joelamichaelis/8x8x8_RGB_LED_CUBE/Documents/Steve Manley Resources/PCB Layouts/Base PCB All Layers with Copper Fill as Viewed from Underneith - Rev 1.1.pdf

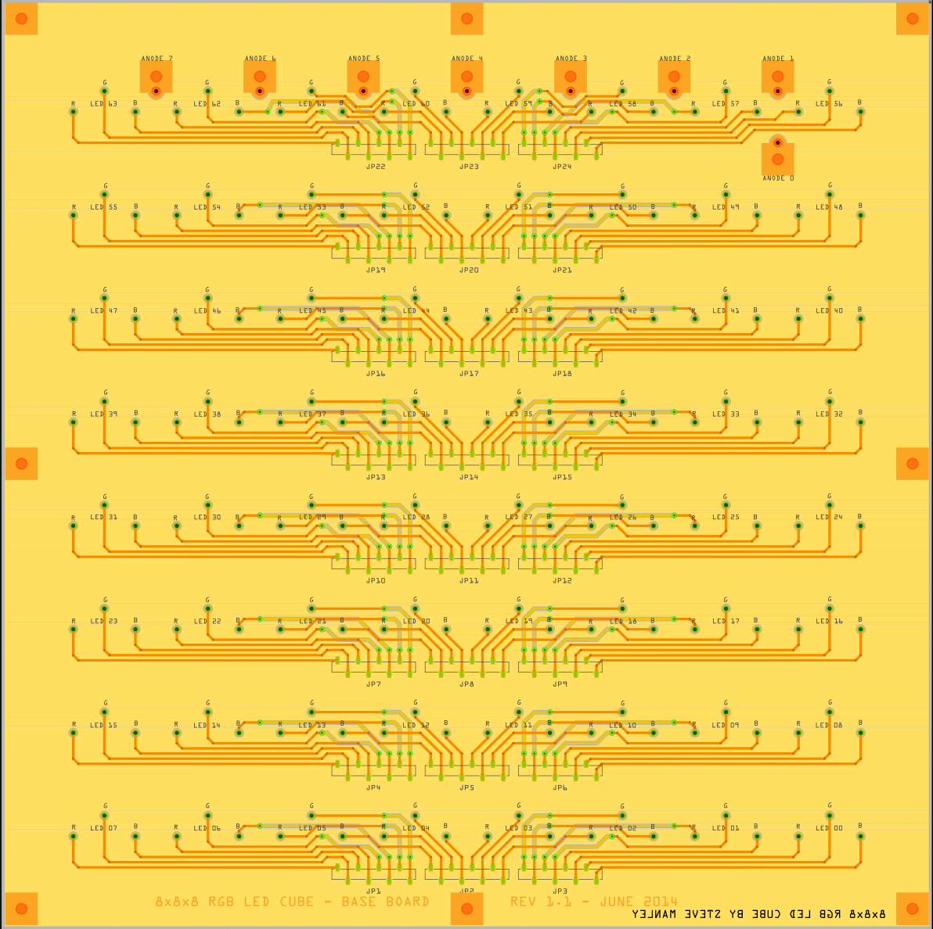
[picture p3: page 1]
