joelamichaelis/8x8x8_RGB_LED_CUBE/Documents/Steve Manley Resources/PCB Layouts/Base PCB Topside with Copper Fill as Viewed from Above - Rev 1.1.pdf

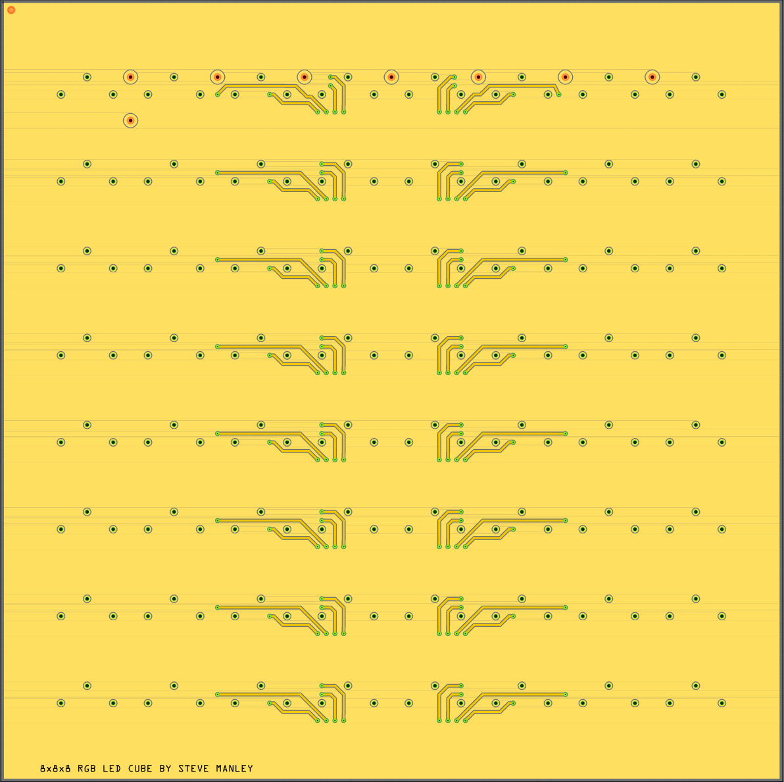
[picture p4: page 1]
