joelamichaelis/8x8x8_RGB_LED_CUBE/Documents/Steve Manley Resources/PCB Layouts/Base PCB Topside without Copper Fill as Viewed from Above - Rev 1.1.pdf

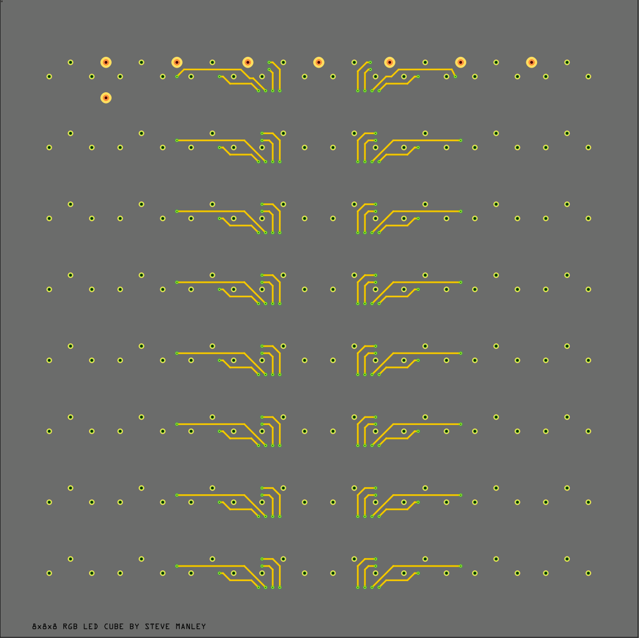
[picture p5: page 1]
