joelamichaelis/8x8x8_RGB_LED_CUBE/Documents/Steve Manley Resources/PCB Layouts/Base PCB Underside as Viewed from Underneith - Rev 1.1.pdf

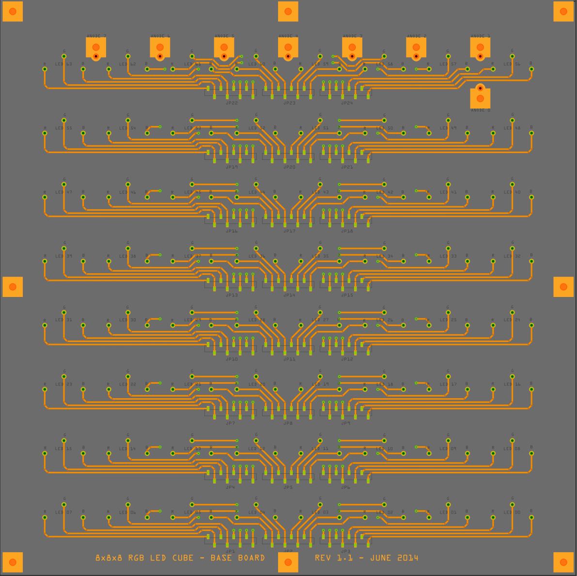
[picture p6: page 1]
