joelamichaelis/8x8x8_RGB_LED_CUBE/Datasheets/Microprocessor/STM32 vs ATmega328P.PNG

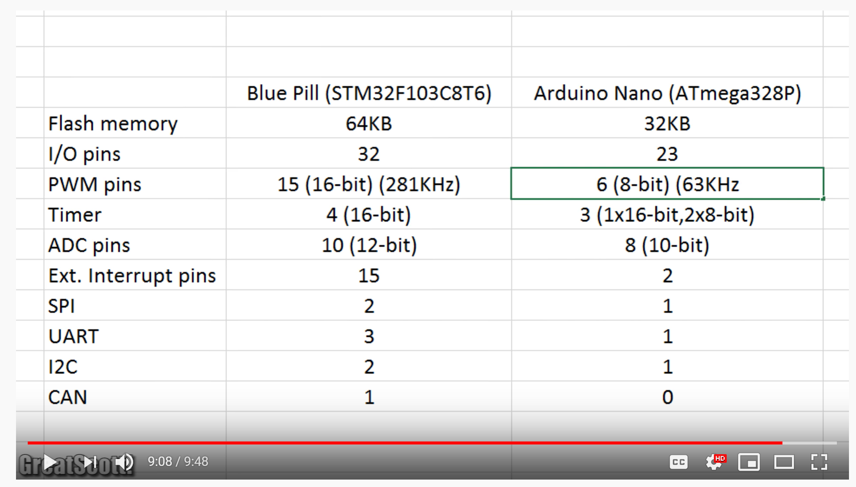
Datasheets/Microprocessor/STM32 vs ATmega328P.PNG
