joelamichaelis/8x8x8_RGB_LED_CUBE/Documents/Misc/firmware alphabet.jpg

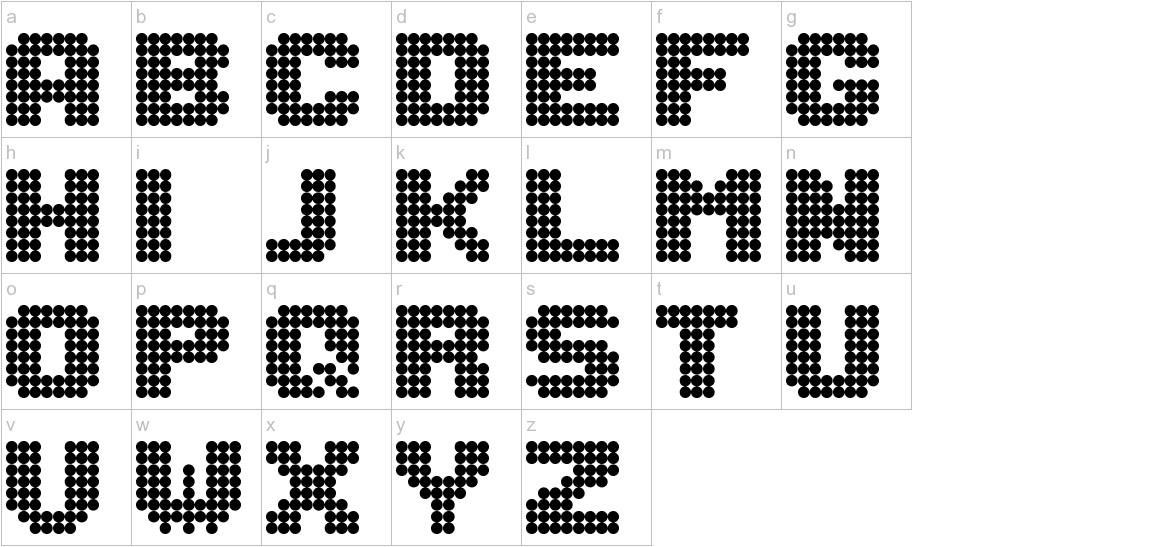
Documents/Misc/firmware alphabet.jpg
