joelamichaelis/8x8x8_RGB_LED_CUBE/Firmware/Misc/I2C_LCD_Development/lcd_addreses.jpg

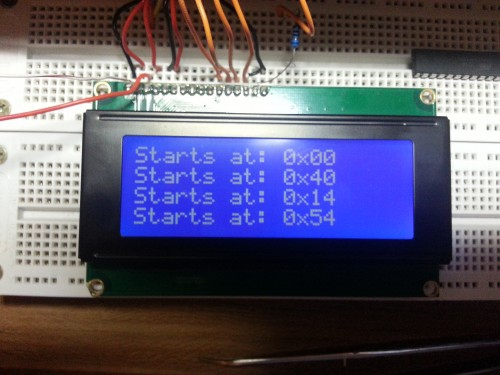
Firmware/Misc/I2C_LCD_Development/lcd_addreses.jpg
