joelamichaelis/8x8x8_RGB_LED_CUBE/Firmware/Misc/STM32 Personal Firmware/cube/USB_OTG_Clock.PNG

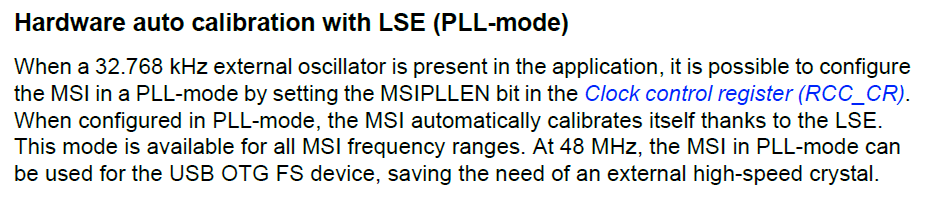
Firmware/Misc/STM32 Personal Firmware/cube/USB_OTG_Clock.PNG
