joelamichaelis/8x8x8_RGB_LED_CUBE/Project Photos/Phase 2 Photos/Mechanical Renders/2020-03-29 CubeBaseFull_FRONT.ipt.png

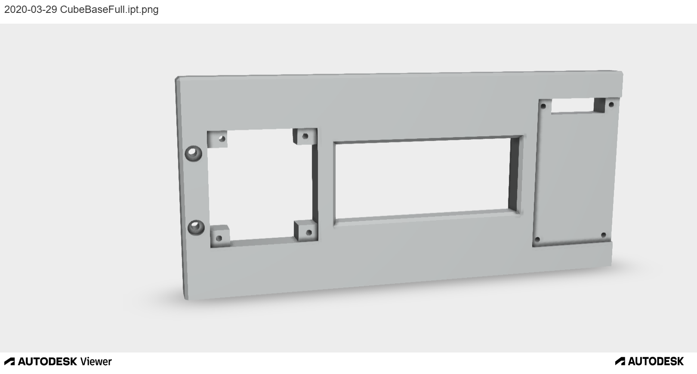
Project Photos/Phase 2 Photos/Mechanical Renders/2020-03-29 CubeBaseFull_FRONT.ipt.png
