joelamichaelis/8x8x8_RGB_LED_CUBE/Project Photos/Phase 2 Photos/Mechanical Renders/2020-04-11 CubeBaseSkeleton_FRONT.png

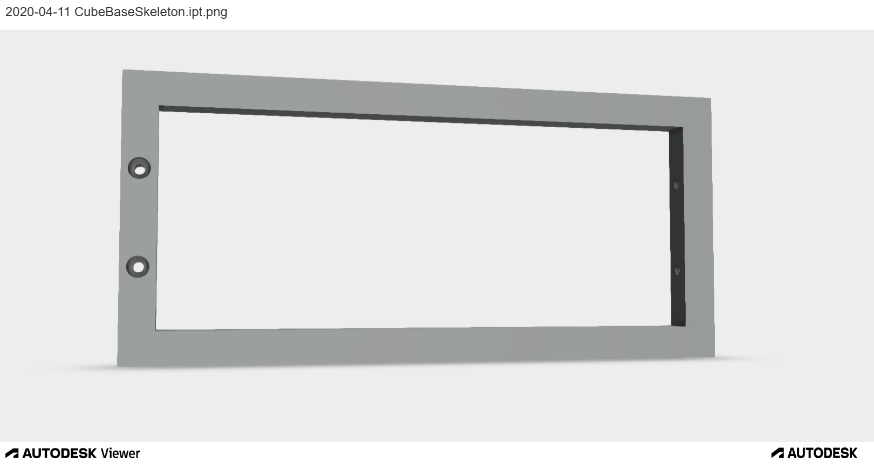
Project Photos/Phase 2 Photos/Mechanical Renders/2020-04-11 CubeBaseSkeleton_FRONT.png
