joelamichaelis/8x8x8_RGB_LED_CUBE/Project Photos/Phase 1 Cube Build/01 LED Bending/20180319_185009.jpg

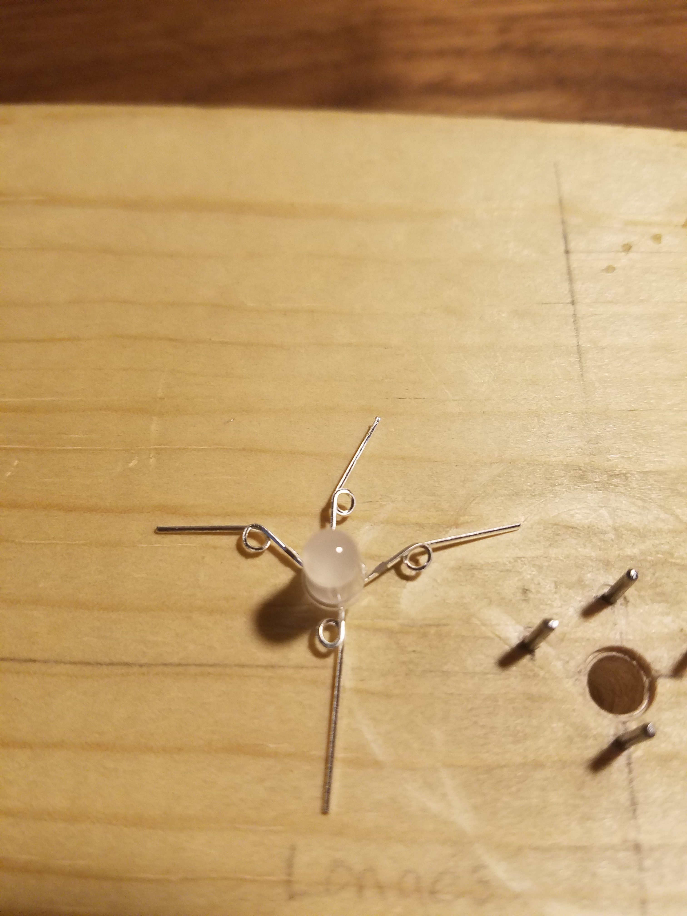
Project Photos/Phase 1 Cube Build/01 LED Bending/20180319_185009.jpg
