joelamichaelis/8x8x8_RGB_LED_CUBE/Project Photos/Phase 1 Cube Build/02 Strip Making/20180319_185600.jpg

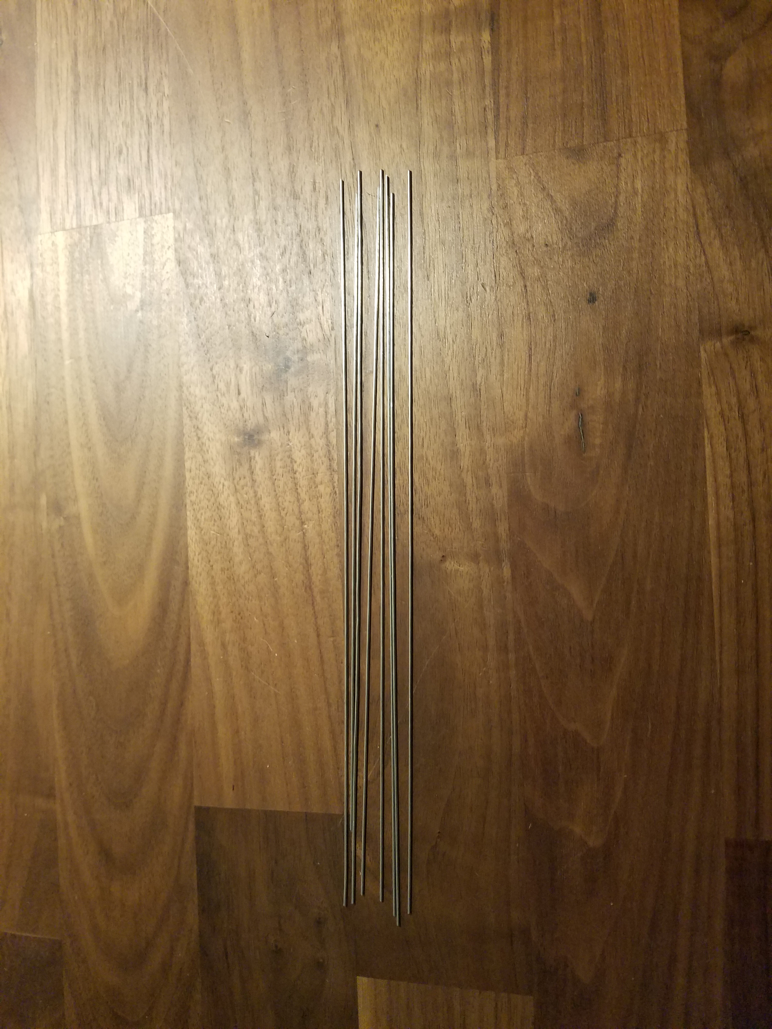
Project Photos/Phase 1 Cube Build/02 Strip Making/20180319_185600.jpg
