joelamichaelis/8x8x8_RGB_LED_CUBE/Project Photos/Phase 2 Photos/Mechanical Renders/CubeAssembly.iam.png

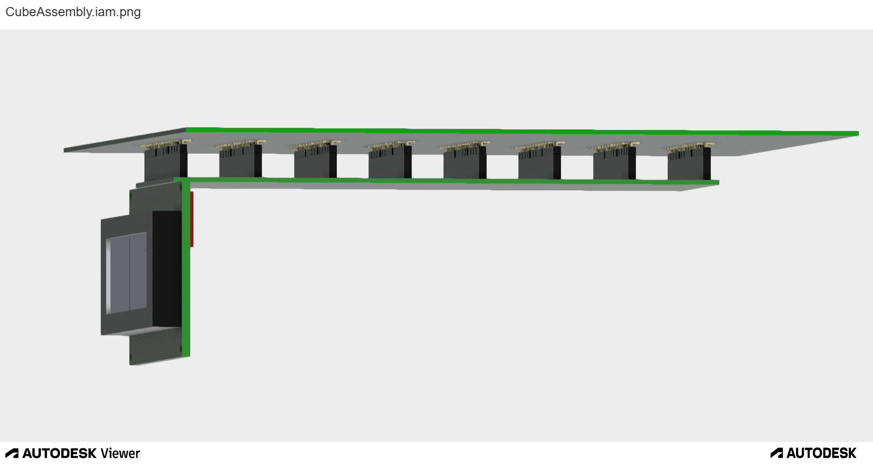
Project Photos/Phase 2 Photos/Mechanical Renders/CubeAssembly.iam.png
