joelamichaelis/8x8x8_RGB_LED_CUBE/Documents/Steve Manley Resources/PCB Layouts/Shift Register Board All Layers without Copper Fills as Viewed from Above - Rev A.pdf

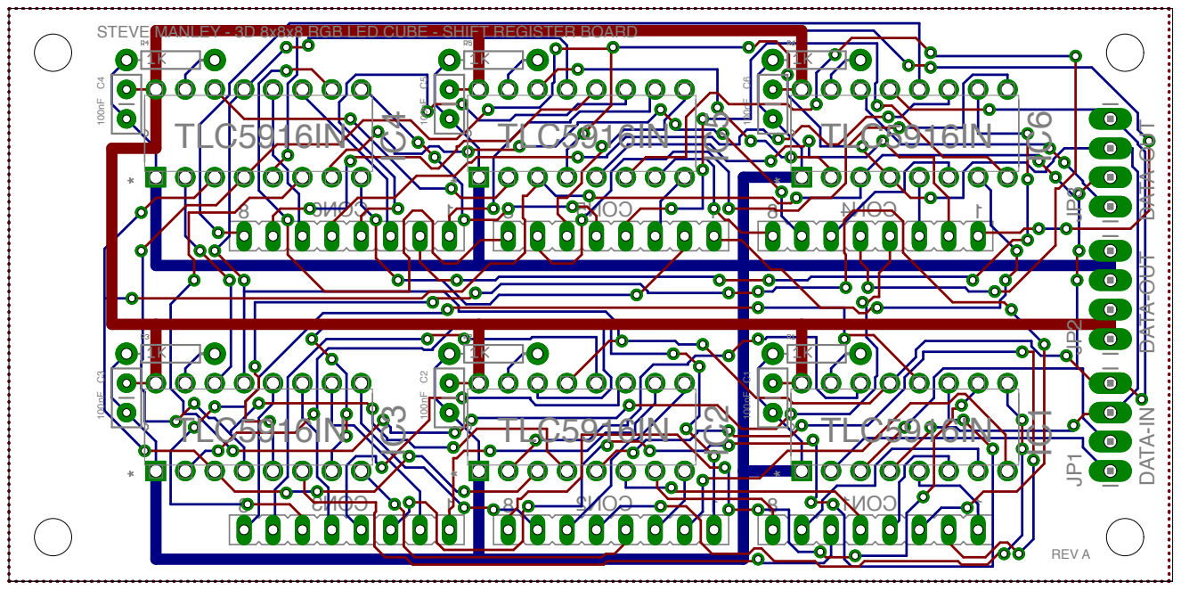
[picture p59: page 1]

STEVE MANLEY - 3D 8x8x8 RGB LED CUBE - SHIFT REGISTER BOARD

DATA-IN DATA-OUT DATA-OUT
