joelamichaelis/8x8x8_RGB_LED_CUBE/Documents/Steve Manley Resources/PCB Layouts/Anode Driver Board All Layers without Copper Fills as Viewed from Above - Rev A.pdf

## D1 X⁵

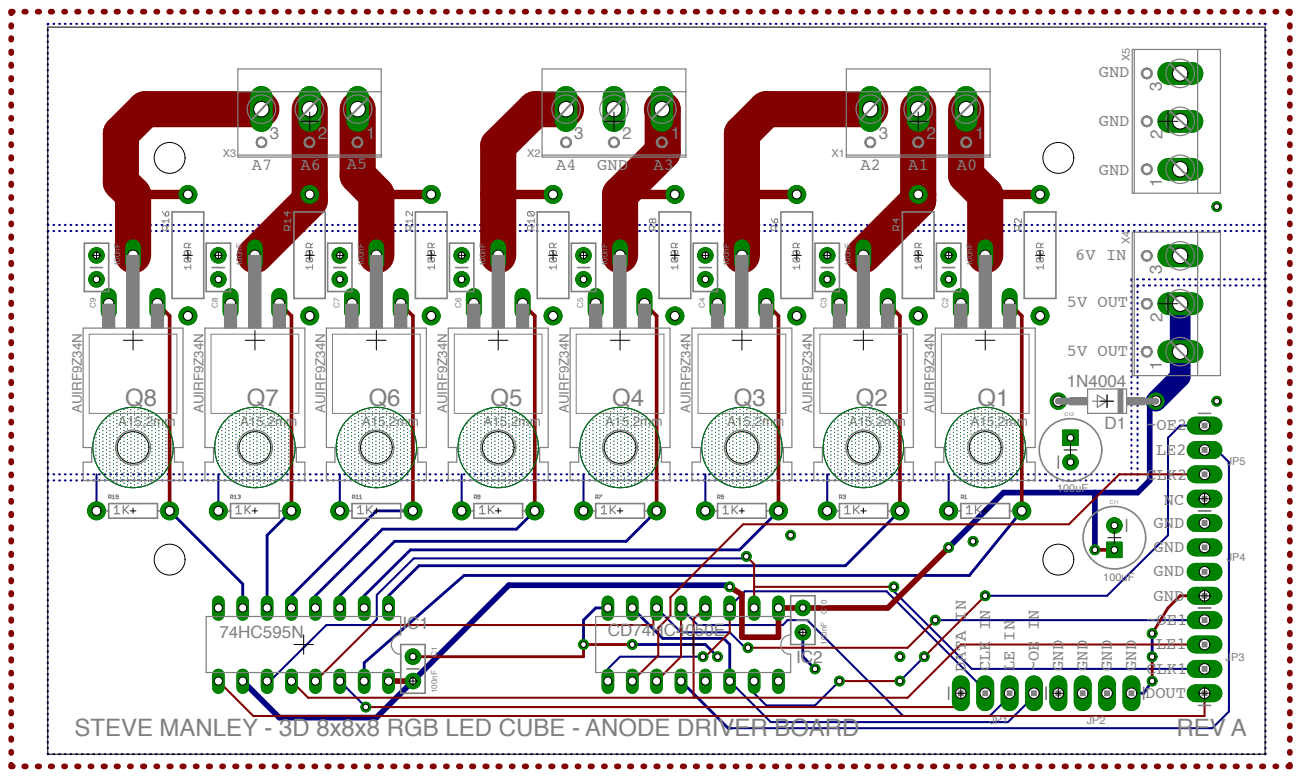
[picture p60: page 1]
