joelamichaelis/8x8x8_RGB_LED_CUBE/Documents/Layout & Schematics/Motherboard_Rev1/SCH-Motherboard_Rev1.pdf

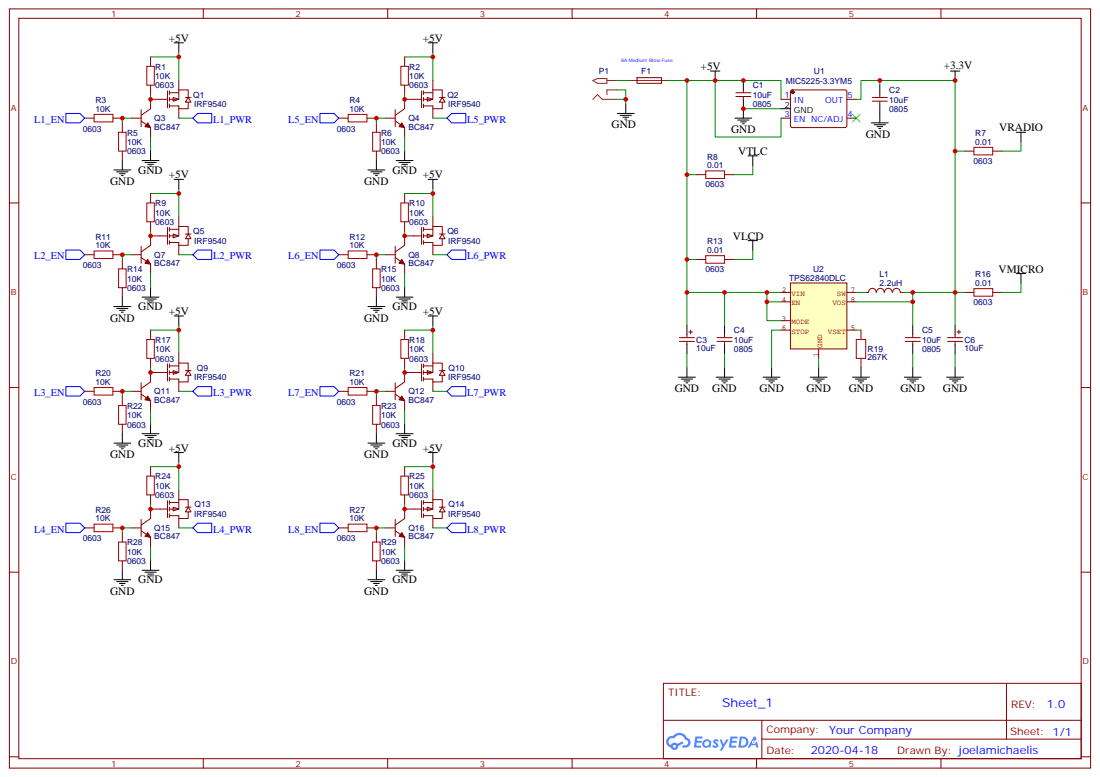
[picture p65: page 1]

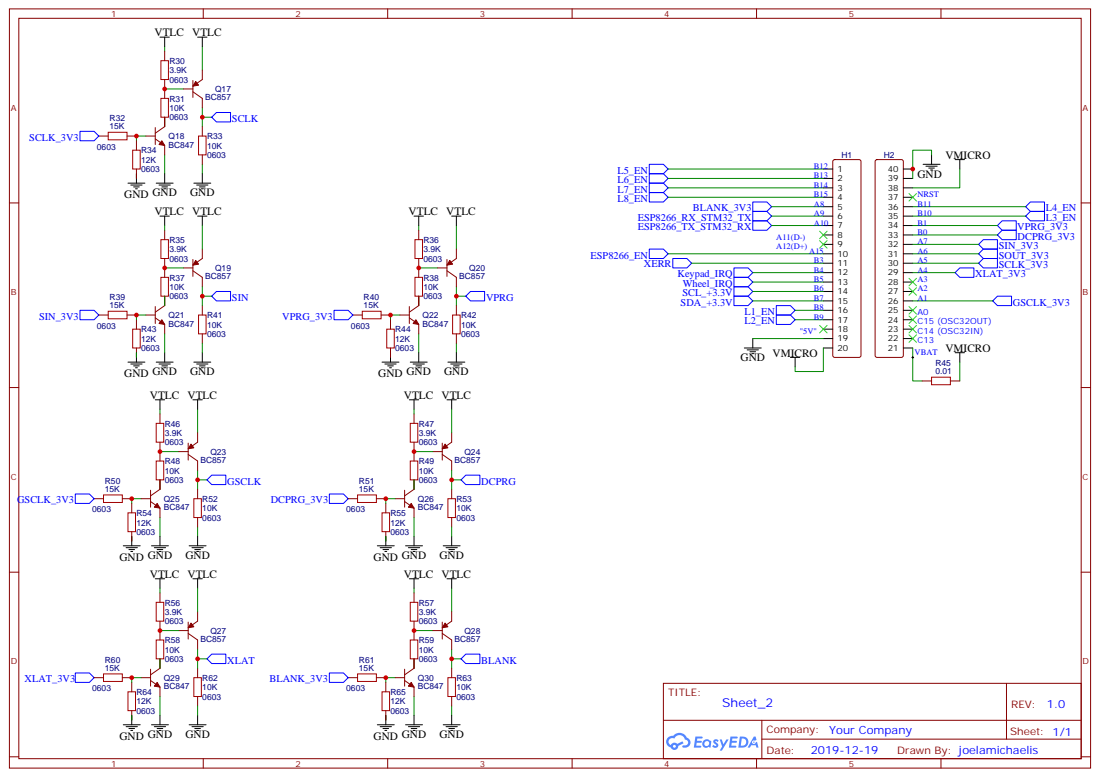
[picture p66: page 2]

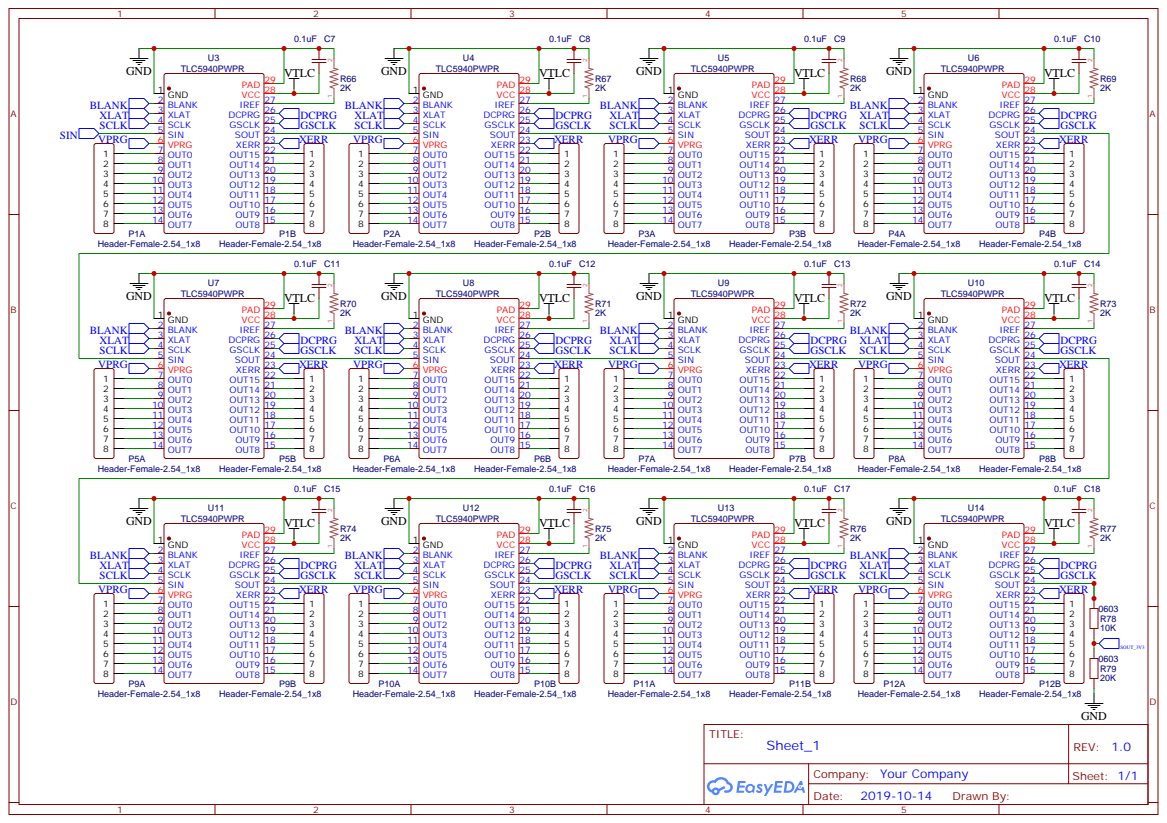
[picture p67: page 3]

## LCD ADDR = 0x27 ESP8266 Connector

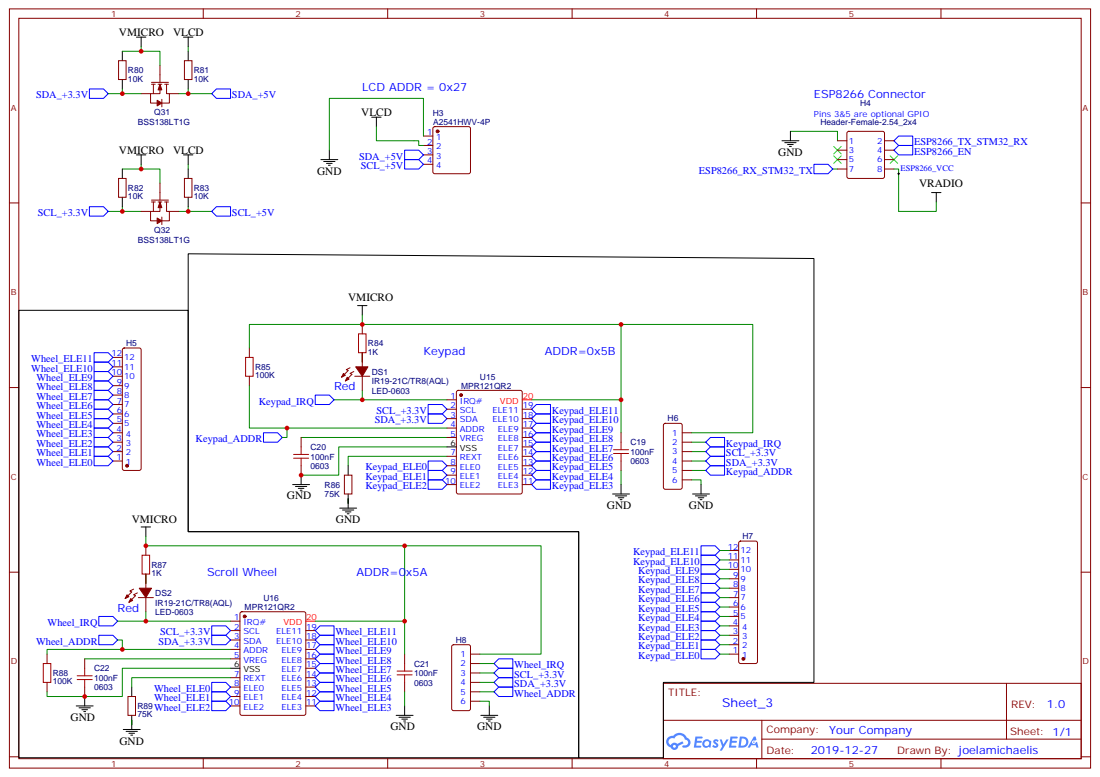
[picture p68: page 4]

Pins 3&5 are optional GPIO
Header-Female-2.54_2x4
