joelamichaelis/8x8x8_RGB_LED_CUBE/Firmware/Misc/2020-11-21 Keil/Inc/mpr121.h

/**
 * MPR121 Library
 *
 * created on: 12/09/18
 * Version: 1.0
 *   
 * Copyright 2012 Waiman Zhao <Binpower@foxmail.com> 
 * Based on previous work by:
 *    Weibo: <http://weibo.com/binpower>
 *    QQ: <93242033>
 *		TaoBao: <http://waiman.taobao.com/>
*/



#ifndef MPR121_h
#define MPR121_h

#include "main.h"
#include "stm32f1xx_hal.h"

/*
#include <Wire.h>
// include types & constants of Wiring core API
#if defined(ARDUINO) && ARDUINO >= 100
	#include "Arduino.h"
#else
	#include <WProgram.h>
	#include <WConstants.h>
#endif
*/

//============ Device Address
// ADD pin is Vcc So address is 0x5B
#define WHEEL_ADDRESS 0x5A // I think this is 0x5A on motherboard rev. 1
#define KEYPAD_ADDRESS 0x5B //// I think this is 0x5B on motherboard rev. 1
static I2C_HandleTypeDef *mpr121_i2cHandle;


// MPR121 Register Defines
#define E0BV	0x1E
#define E1BV	0x1F
#define E2BV	0x20
#define E3BV	0x21
#define E4BV	0x22
#define E5BV	0x23
#define E6BV	0x24
#define E7BV	0x25
#define E8BV	0x26
#define E9BV	0x27
#define E10BV	0x28
#define E11BV	0x29
#define E12BV	0x2A


#define MHD_R	0x2B
#define NHD_R	0x2C
#define	NCL_R 0x2D
#define	FDL_R	0x2E
#define	MHD_F	0x2F
#define	NHD_F	0x30
#define	NCL_F	0x31
#define	FDL_F	0x32


#define	ELE0_T	0x41
#define	ELE0_R	0x42
#define	ELE1_T	0x43
#define	ELE1_R	0x44
#define	ELE2_T	0x45
#define	ELE2_R	0x46
#define	ELE3_T	0x47
#define	ELE3_R	0x48
#define	ELE4_T	0x49
#define	ELE4_R	0x4A
#define	ELE5_T	0x4B
#define	ELE5_R	0x4C
#define	ELE6_T	0x4D
#define	ELE6_R	0x4E
#define	ELE7_T	0x4F
#define	ELE7_R	0x50
#define	ELE8_T	0x51
#define	ELE8_R	0x52
#define	ELE9_T	0x53
#define	ELE9_R	0x54
#define	ELE10_T	0x55
#define	ELE10_R	0x56
#define	ELE11_T	0x57
#define	ELE11_R	0x58


#define	AFE1_CFG	0x5C
#define	AFE2_CFG	0x5D
#define	ELE_CFG		0x5E


#define GPIO_CTRL0	0x73
#define	GPIO_CTRL1	0x74
#define GPIO_DATA	0x75
#define	GPIO_DIR	0x76
#define	GPIO_EN		0x77
#define	GPIO_SET	0x78
#define	GPIO_CLEAR	0x79
#define	GPIO_TOGGLE	0x7A


#define	ATO_CFG0	0x7B
#define	ATO_CFGU	0x7D
#define	ATO_CFGL	0x7E
#define	ATO_CFGT	0x7F
#define	RES_CF          0x80

// Global Constants	//隔住阻焊层
#define TOU_THRESH	0x06
#define	REL_THRESH	0x03
#define	START_BV	0x90
// Global Constants	//隔住0.5mm
//#define TOU_THRESH	0x06
//#define	REL_THRESH	0x03




void mpr121_init(I2C_HandleTypeDef *hi2c, uint8_t mpr121Address, I2C_HandleTypeDef *pI2cHandle);
void mpr121_write(I2C_HandleTypeDef *hi2c, uint8_t mpr121Address, uint8_t reg,uint8_t data);
void mpr121_read(I2C_HandleTypeDef *hi2c, uint8_t mpr121Address, uint8_t reg,uint8_t length,uint8_t *ReturnData);

uint16_t mpr121_touch(I2C_HandleTypeDef *hi2c, uint8_t mpr121Address);
uint8_t mpr121_wheelKey(I2C_HandleTypeDef *hi2c, uint8_t mpr121Address);
uint8_t mpr121_keyPad(I2C_HandleTypeDef *hi2c, uint8_t mpr121Address);
	



#endif
