joelamichaelis/8x8x8_RGB_LED_CUBE/Documents/Steve Manley Resources/Arduino Sketches/Cube_Test_V0.0/Cube0_0/Cube0_0.ino

// ===================================================================================
// Title:    3D 8x8x8 RGB LED CUBE by STEVE MANLEY
// Function: Cube
// Board:    Arduino Uno R3
// Version:  1.0
// Author:   Steve Manley
// Date:     5th September 2014
// License:  The MIT License (See full license at the bottom of this file)
// Notes:    First experiments with dividing 8x8 RGB LED Panels using multiplexing
//           and interrupt timers. Starts of scrolling a message, then repeats a 
//           sequence of different routines for displaying patterns and fills.
// ===================================================================================

#include "SPI.h"

#define SPI_SCK         13                 // SPI clock    - must be pin 13
#define SPI_MOSI        11                 // SPI data out - must be pin 11
#define SR_LATCH         3                 // shift register latch         - any non SPI pin
#define SR_BLANK         2                 // shift register output enable - any non SPI pin
#define TD1             80                 // time delay 1 - 100ms
#define TD2           3000                 // time delay 2 -   3 seconds
#define TD3           1000                 // time delay 3 -   1 second
#define TD4             20                 // time delay 4 -  20ms
#define TD5            400                 // time delay 5 - 400ms
#define TD6            120                 // time delay 5 - 400ms
#define TD7            100                 // time delay 5 - 400ms


// =====================================================================================================
// variables used by Inturrupt Service Routine (ISR), must be volatile
// =====================================================================================================
volatile byte shiftRegisterRed[64];         // red   shift register data, 8 bytes, 1 byte per common anode
volatile byte shiftRegisterGrn[64];         // green shift register data, 8 bytes, 1 byte per common anode
volatile byte shiftRegisterBlu[64];         // blue  shift register data, 8 bytes, 1 byte per common anode
volatile byte anodeIndex   = 0;            // keeps track of which common anode is active
volatile byte anodeLevel[] = {             // used by 74HC595N shift register to control the anode multiplexing
              B11111110,                   // This is not an efficient use of variable memory, but what the heck!
              B11111101,                   // at least it shows how the anode multiplexing is done.
              B11111011, 
              B11110111, 
              B11101111, 
              B11011111, 
              B10111111,
              B01111111}; 
         byte colours[] = { 1, 2, 4, 3, 6, 5, 7 };

// =====================================================================================================
// font definition
// =====================================================================================================
char font8x8_basic[95][8] = {
  {0x00, 0x00, 0x00, 0x00, 0x00, 0x00, 0x00, 0x00},   // Ascii ( )
  {0x04, 0x04, 0x04, 0x04, 0x04, 0x00, 0x04, 0x00},   // Ascii (!)
  {0x14, 0x14, 0x14, 0x00, 0x00, 0x00, 0x00, 0x00},   // Ascii (")
  {0x14, 0x14, 0x3E, 0x14, 0x3E, 0x14, 0x14, 0x00},   // Ascii (#)
  {0x08, 0x3C, 0x0A, 0x1C, 0x28, 0x1E, 0x08, 0x00},   // Ascii ($)
  {0x06, 0x26, 0x10, 0x08, 0x04, 0x32, 0x30, 0x00},   // Ascii (%)
  {0x0C, 0x12, 0x0A, 0x04, 0x2A, 0x12, 0x2C, 0x00},   // Ascii (&)
  {0x0C, 0x08, 0x04, 0x00, 0x00, 0x00, 0x00, 0x00},   // Ascii (')
  {0x08, 0x04, 0x02, 0x02, 0x02, 0x04, 0x08, 0x00},   // Ascii (()
  {0x02, 0x04, 0x08, 0x08, 0x08, 0x04, 0x02, 0x00},   // Ascii ())
  {0x00, 0x14, 0x08, 0x3E, 0x08, 0x14, 0x00, 0x00},   // Ascii (*)
  {0x00, 0x08, 0x08, 0x3E, 0x08, 0x08, 0x00, 0x00},   // Ascii (+)
  {0x00, 0x00, 0x00, 0x00, 0x00, 0x06, 0x04, 0x02},   // Ascii (,)
  {0x00, 0x00, 0x00, 0x3E, 0x00, 0x00, 0x00, 0x00},   // Ascii (-)
  {0x00, 0x00, 0x00, 0x00, 0x00, 0x06, 0x06, 0x00},   // Ascii (.)
  {0x00, 0x20, 0x10, 0x08, 0x04, 0x02, 0x00, 0x00},   // Ascii (/)
  {0x1C, 0x22, 0x32, 0x2A, 0x26, 0x22, 0x1C, 0x00},   // Ascii (0)
  {0x08, 0x0C, 0x08, 0x08, 0x08, 0x08, 0x1C, 0x00},   // Ascii (1)
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
  {0x00, 0x00, 0x0E, 0x12, 0x12, 0x0E, 0x02, 0x02},   // Ascii (p)
  {0x00, 0x00, 0x1C, 0x12, 0x12, 0x1C, 0x10, 0x10},   // Ascii (q)
  {0x00, 0x00, 0x14, 0x0C, 0x04, 0x04, 0x04, 0x00},   // Ascii (r)
  {0x00, 0x00, 0x1C, 0x02, 0x0C, 0x10, 0x0E, 0x00},   // Ascii (s)
  {0x04, 0x04, 0x0E, 0x04, 0x04, 0x04, 0x0C, 0x00},   // Ascii (t)
  {0x00, 0x00, 0x12, 0x12, 0x12, 0x12, 0x1C, 0x00},   // Ascii (u)
  {0x00, 0x00, 0x22, 0x22, 0x22, 0x14, 0x08, 0x00},   // Ascii (v)
  {0x00, 0x00, 0x22, 0x22, 0x2A, 0x2A, 0x14, 0x00},   // Ascii (w)
  {0x00, 0x00, 0x22, 0x14, 0x08, 0x14, 0x22, 0x00},   // Ascii (x)
  {0x00, 0x00, 0x12, 0x12, 0x12, 0x1C, 0x10, 0x0C},   // Ascii (y)
  {0x00, 0x00, 0x3E, 0x10, 0x08, 0x04, 0x3E, 0x00},   // Ascii (z)
  {0x08, 0x04, 0x04, 0x02, 0x04, 0x04, 0x08, 0x00},   // Ascii ({)
  {0x04, 0x04, 0x04, 0x04, 0x04, 0x04, 0x04, 0x00},   // Ascii (|)
  {0x02, 0x04, 0x04, 0x08, 0x04, 0x04, 0x02, 0x00},   // Ascii (})
  {0x2C, 0x12, 0x00, 0x00, 0x00, 0x00, 0x00, 0x00}};  // Ascii (~)



// =====================================================================================================
// ~~~ START of SETUP ~~~
// =====================================================================================================
void setup() {

  // set up IO pins as outputs
  // -------------------------------------------------------------
  pinMode(SPI_SCK,  OUTPUT);
  pinMode(SPI_MOSI, OUTPUT);
  pinMode(SR_LATCH, OUTPUT);
  pinMode(SR_BLANK, OUTPUT);

  digitalWrite(SR_BLANK, HIGH);              // temporarily disable all shift register outputs
  digitalWrite(SR_LATCH,  LOW);              // set shift register latch to initial state

  // set up Timer 2 for 8KHz (125uS) interrupt 
  // code example from Amanda Ghassaei 
  // http://www.instructables.com/id/Arduino-Timer-Interrupts/?ALLSTEPS
  // ------------------------------------------------------------------
    cli();                                   // stop interrupts
    TCCR2A  =   0;                           // set entire TCCR2A register to 0
    TCCR2B  =   0;                           // same for TCCR2B
    TCNT2   =   0;                           // initialize counter value to 0
    OCR2A   = 249;                           // Set compare match register for 16KHz. Increments calculated as follows:
                                             // Arduino clk frequency 16MHz / (required frequency * Prescaler of 8) - 1, Result must be < 256.
                                             // So for this instance we calculate 16,000,000 / (8,000 * 8) - 1 = 249
    TCCR2A |= (1 << WGM21);                  // turn on CTC mode
    TCCR2B |= (1 << CS21);                   // Set CS21 bit for 8 pre-scalar
    TIMSK2 |= (1 << OCIE2A);                 // enable timer compare interrupt
    sei();                                   // allow interrupts
  // end code example from Amanda Ghassaei
  // -------------------------------------------------------------
  
  // initialise SPI
  // -------------------------------------------------------------
  SPI.setDataMode    (SPI_MODE0     );       // mode 0 rising edge of data, keep clock low
  SPI.setBitOrder    (MSBFIRST      );       // most significant bit first
  SPI.setClockDivider(SPI_CLOCK_DIV2);       // run the data in at 16MHz/2 - 8MHz (max speed)
  SPI.begin();                               // start up SPI

  // initialise Serial Port for de-bugging
  // -------------------------------------------------------------
  Serial.begin  (115200 );                   // set up serial port for 115200 baud rate
  Serial.println("Start");                   // display Start in Terminal Window

  randomSeed(analogRead(0));                 // set random seed

  // display some text, only runs once
  // -------------------------------------------------------------
  //displaySomeText("WELCOME TO THE 8x8 RGB LED PANEL TESTING... ", TD5);
}
// ====================
// ~~~ END of SETUP ~~~
// ====================


byte colourIndex = 0; 

// =====================================================================================================
// ~~~ START of LOOP ~~~
// =====================================================================================================
void loop() {
  
//  while (1) {  setPixel(0,0,0,1,0,0); setPixel(7,2,0,0,1,0); setPixel(7,4,7,0,0,1); setPixel(0,6,7,1,1,0); }
  
//while(1){
//drawRectangleFilled(0, 0, 0, 7, 7, 7, 1, 0, 0);  // clear the cube
//delay(1000);
//drawRectangleFilled(0, 0, 0, 7, 7, 7, 0, 1, 0);  // clear the cube
//delay(1000);
//drawRectangleFilled(0, 0, 0, 7, 7, 7, 0, 0, 1);  // clear the cube
//delay(1000);
//drawRectangleFilled(0, 0, 0, 7, 7, 7, 0, 0, 0);  // clear the cube
//delay(500000);
//}
// Outline expanding contracting cubes

  for (int i = 0; i < 8; i++) {
    drawRectangleOutline(0, 0, 0, i, i, i, 1, 0, 0); delay (TD1);
    drawRectangleOutline(0, 0, 0, i, i, i, 0, 0, 0);
  }

  for (int i = 0; i < 8; i++) {
    drawRectangleOutline(i, i, i, 7, 7, 7, 1, 0, 0); delay (TD1);
    drawRectangleOutline(i, i, i, 7, 7, 7, 0, 0, 0);
  }

  for (int i = 0; i < 8; i++) {
    drawRectangleOutline(0, 0, 7 - i, i, i, 7, 0, 0, 1); delay (TD1);
    drawRectangleOutline(0, 0, 7 - i, i, i, 7, 0, 0, 0);
  }
  for (int i = 0; i < 8; i++) {
    drawRectangleOutline(i, i, 0, 7, 7, 7 - i, 0, 0, 1); delay (TD1);
    drawRectangleOutline(i, i, 0, 7, 7, 7 - i, 0, 0, 0);
  }

  for (int i = 0; i < 8 ; i++) {
    drawRectangleOutline(7 - i, 0, 0, 7, i, i, 0, 1, 0); delay (TD1);
    drawRectangleOutline(7 - i, 0, 0, 7, i, i, 0, 0, 0);
  }
  for (int i = 7; i > -1; i--) {
    drawRectangleOutline(0, 7 - i, 7 - i, i, 7, 7, 0, 1, 0); delay (TD1);
    drawRectangleOutline(0, 7 - i, 7 - i, i, 7, 7, 0, 0, 0);
  }

  for (int i = 0; i < 8; i++) {
    drawRectangleOutline(0, 7 - i, 0, i, 7, i, 1, 1, 1); delay (TD1);
    drawRectangleOutline(0, 7 - i, 0, i, 7, i, 0, 0, 0);
  }
  for (int i = 0; i < 8; i++) {
    drawRectangleOutline(i, 0, i, 7, 7 - i, 7, 1, 1, 1); delay (TD1);
    drawRectangleOutline(i, 0, i, 7, 7 - i, 7, 0, 0, 0);
  }

// small r cube spin
  for (int i = 0; i < 6; i++) {
    drawRectangleOutline(i, 0, 0, i + 1, 1, 1, 1, 0, 0); delay (TD1);
    drawRectangleOutline(i, 0, 0, i,     1, 1, 0, 0, 0);
  }

  for (int i = 0; i < 6; i++) {
    drawRectangleOutline(6, i, 0, 7, i + 1, 1, 1, 0, 0); delay (TD1);
    drawRectangleOutline(6, i, 0, 7, i,     1, 0, 0, 0);
  }

  for (int i = 0; i < 6; i++) {
    drawRectangleOutline(6 - i, 6, 0, 7 - i, 7, 1, 1, 0, 0); delay (TD1);
    drawRectangleOutline(7 - i, 6, 0, 7 - i, 7, 1, 0, 0, 0);
  }

  for (int i = 0; i < 6; i++) {
    drawRectangleOutline(0, 6 - i, 0, 1, 7 - i, 1, 1, 0, 0); delay (TD1);
    drawRectangleOutline(0, 7 - i, 0, 1, 7 - i, 1, 0, 0, 0);
  }

// small rg cube spin
  for (int i = 0; i < 6; i++) {
    drawRectangleOutline(i, 0, 0, i + 1, 1, 1, 1, 0, 0);
    drawRectangleOutline(6, i, 2, 7, i + 1, 3, 0, 1, 0); delay (TD1);
    drawRectangleOutline(6, i, 2, 7, i, 3, 0, 0, 0);
    drawRectangleOutline(i, 0, 0, i, 1, 1, 0, 0, 0);
  }

  for (int i = 0; i < 6; i++) {
    drawRectangleOutline(6, i, 0, 7, i + 1, 1, 1, 0, 0);
    drawRectangleOutline(6 - i, 6, 2, 7 - i, 7, 3, 0, 1, 0); delay (TD1);
    drawRectangleOutline(7 - i, 6, 2, 7 - i, 7, 3, 0, 0, 0);
    drawRectangleOutline(6, i, 0, 7, i, 1, 0, 0, 0);
  }

  for (int i = 0; i < 6; i++) {
    drawRectangleOutline(6 - i, 6, 0, 7 - i, 7, 1, 1, 0, 0);
    drawRectangleOutline(0, 6 - i, 2, 1, 7 - i, 3, 0, 1, 0); delay (TD1);
    drawRectangleOutline(0, 7 - i, 2, 1, 7 - i, 3, 0, 0, 0);
    drawRectangleOutline(7 - i, 6, 0, 7 - i, 7, 1, 0, 0, 0);
  }

  for (int i = 0; i < 6; i++) {
    drawRectangleOutline(0, 6 - i, 0, 1, 7 - i, 1, 1, 0, 0);
    drawRectangleOutline(i, 0, 2, i + 1, 1, 3, 0, 1, 0); delay (TD1);
    drawRectangleOutline(i, 0, 2, i, 1, 3, 0, 0, 0);
    drawRectangleOutline(0, 7 - i, 0, 1, 7 - i, 1, 0, 0, 0);
  }

// small rgb cube spin
  for (int i = 0; i < 6; i++) {
    drawRectangleOutline(i, 0, 0, i + 1, 1, 1, 1, 0, 0);
    drawRectangleOutline(6, i, 2, 7, i + 1, 3, 0, 1, 0);
    drawRectangleOutline(6 - i, 6, 4, 7 - i, 7, 5, 0, 0, 1); delay (TD1);
    drawRectangleOutline(7 - i, 6, 4, 7 - i, 7, 5, 0, 0, 0);
    drawRectangleOutline(6, i, 2, 7, i, 3, 0, 0, 0);
    drawRectangleOutline(i, 0, 0, i, 1, 1, 0, 0, 0);
  }

  for (int i = 0; i < 6; i++) {
    drawRectangleOutline(6, i, 0, 7, i + 1, 1, 1, 0, 0);
    drawRectangleOutline(6 - i, 6, 2, 7 - i, 7, 3, 0, 1, 0);
    drawRectangleOutline(0, 6 - i, 4, 1, 7 - i, 5, 0, 0, 1); delay (TD1);
    drawRectangleOutline(0, 7 - i, 4, 1, 7 - i, 5, 0, 0, 0);
    drawRectangleOutline(7 - i, 6, 2, 7 - i, 7, 3, 0, 0, 0);
    drawRectangleOutline(6, i, 0, 7, i, 1, 0, 0, 0);
  }

  for (int i = 0; i < 6; i++) {
    drawRectangleOutline(6 - i, 6, 0, 7 - i, 7, 1, 1, 0, 0);
    drawRectangleOutline(0, 6 - i, 2, 1, 7 - i, 3, 0, 1, 0);
    drawRectangleOutline(i, 0, 4, i + 1, 1, 5, 0, 0, 1); delay (TD1);
    drawRectangleOutline(i, 0, 4, i, 1, 5, 0, 0, 0);
    drawRectangleOutline(0, 7 - i, 2, 1, 7 - i, 3, 0, 0, 0);
    drawRectangleOutline(7 - i, 6, 0, 7 - i, 7, 1, 0, 0, 0);
  }

  for (int i = 0; i < 6; i++) {
    drawRectangleOutline(0, 6 - i, 0, 1, 7 - i, 1, 1, 0, 0);
    drawRectangleOutline(i, 0, 2, i + 1, 1, 3, 0, 1, 0);
    drawRectangleOutline(6, i, 4, 7, i + 1, 5, 0, 0, 1); delay (TD1);
    drawRectangleOutline(6, i, 4, 7, i, 5, 0, 0, 0);
    drawRectangleOutline(i, 0, 2, i, 1, 3, 0, 0, 0);
    drawRectangleOutline(0, 7 - i, 0, 1, 7 - i, 1, 0, 0, 0);
  }

// small rgby cube spin
  for(int l = 0; l < 1; l++) {
  
    for (int i = 0; i < 6; i++) {
      drawRectangleOutline(i, 0, 0, i + 1, 1, 1, 1, 0, 0);
      drawRectangleOutline(6, i, 2, 7, i + 1, 3, 0, 1, 0);
      drawRectangleOutline(6 - i, 6, 4, 7 - i, 7, 5, 0, 0, 1);
      drawRectangleOutline(0, 6 - i, 6, 1, 7 - i, 7, 1, 1, 0); delay (TD1);
      drawRectangleOutline(0, 7 - i, 6, 1, 7 - i, 7, 0, 0, 0);
      drawRectangleOutline(7 - i, 6, 4, 7 - i, 7, 5, 0, 0, 0);
      drawRectangleOutline(6, i, 2, 7, i, 3, 0, 0, 0);
      drawRectangleOutline(i, 0, 0, i, 1, 1, 0, 0, 0);
    }
  
    for (int i = 0; i < 6; i++) {
      drawRectangleOutline(6, i, 0, 7, i + 1, 1, 1, 0, 0);
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
//        setPixel(y, z, x, 0, 0, 0);
//      }
//    }
//  }
//
//  for (int x = 0; x < 8; x++) { 
//    for (int y = 0; y < 8; y++) { 
//      delay(50);
//      for (int z = 0; z < 8; z++) { 
//        setPixel(z, x, y, 1, 0, 1);
//      }
//    }
//  }







  for (int i = 0; i < 8; i++) { 
    yzPlaneFill(i, colours[0] ); 
    delay(TD1); 
    yzPlaneFill(i, 0);  }
  for (int i = 6; i > -1; i--) { 
    yzPlaneFill(i, colours[0] ); 
    delay(TD1); 
    yzPlaneFill(i, 0);  }

  for (int i = 0; i < 8; i++) { 
    xyPlaneFill(i, colours[1] ); 
    delay(TD1); 
    xyPlaneFill(i, 0);  }
  for (int i = 6; i > -1; i--) {  
    xyPlaneFill(i, colours[1] ); 
    delay(TD1); 
    xyPlaneFill(i, 0);  }

  for (int i = 0; i < 8; i++) {
    xzPlaneFill(i, colours[2] ); 
    delay(TD1); 
    xzPlaneFill(i, 0);  }
  for (int i = 6; i > -1; i--) { 
    xzPlaneFill(i, colours[2] ); 
    delay(TD1); 
    xzPlaneFill(i, 0);  }

  for (int i = 0; i < 8; i++) { 
    yzPlaneFill(i, colours[0] );
    xyPlaneFill(i, colours[1] );
    delay(TD1); 
    yzPlaneFill(i, 0);
    xyPlaneFill(i, 0);  }
//  for (int i = 6; i > 0; i--) {
//    yzPlaneFill(i, colours[0] );
//    xyPlaneFill(i, colours[1] );
//    delay(TD1); 
//    yzPlaneFill(i, 0);
//    xyPlaneFill(i, 0);  }
  
  for (int i = 0; i < 8; i++) { 
    yzPlaneFill(i, colours[0] ); 
    xzPlaneFill(i, colours[2] );
    delay(TD1); 
    yzPlaneFill(i, 0);
    xzPlaneFill(i, 0);  }
//  for (int i = 6; i > 0; i--) {
//    yzPlaneFill(i, colours[0] ); 
//    xzPlaneFill(i, colours[2] );
//    delay(TD1); 
//    yzPlaneFill(i, 0);
//    xzPlaneFill(i, 0);  }
    
  for (int i = 0; i < 8; i++) { 
    xyPlaneFill(i, colours[1] ); 
    xzPlaneFill(i, colours[2] );
    delay(TD1); 
    xyPlaneFill(i, 0);
    xzPlaneFill(i, 0);    }
//  for (int i = 6; i > 0; i--) {
//    xyPlaneFill(i, colours[1] ); 
//    xzPlaneFill(i, colours[2] );
//    delay(TD1); 
//    xyPlaneFill(i, 0);
//    xzPlaneFill(i, 0);    }
    
  for (int i = 0; i < 8; i++) { 
    yzPlaneFill(i, colours[0] );
    xyPlaneFill(i, colours[1] ); 
    xzPlaneFill(i, colours[2] );
    delay(TD1); 
    yzPlaneFill(i, 0);
    xyPlaneFill(i, 0);
    xzPlaneFill(i, 0);  }
  for (int i = 6; i > 0; i--) { 
    yzPlaneFill(i, colours[0] );
    xyPlaneFill(i, colours[1] ); 
    xzPlaneFill(i, colours[2] );
    delay(TD1); 
    yzPlaneFill(i, 0);
    xyPlaneFill(i, 0);
    xzPlaneFill(i, 0);  }


    drawRectangleSides(3, 3, 3, 4, 4, 4, 1, 0, 0);
    drawRectangleSides(2, 2, 2, 5, 5, 5, 0, 0, 0);
    drawRectangleSides(1, 1, 1, 6, 6, 6, 0, 0, 0);
    drawRectangleSides(0, 0, 0, 7, 7, 7, 0, 0, 0); delay(TD6);
    
    drawRectangleSides(3, 3, 3, 4, 4, 4, 1, 0, 0);
    drawRectangleSides(2, 2, 2, 5, 5, 5, 1, 0, 0);
    drawRectangleSides(1, 1, 1, 6, 6, 6, 0, 0, 0);
    drawRectangleSides(0, 0, 0, 7, 7, 7, 0, 0, 0); delay(TD6);
    
    drawRectangleSides(3, 3, 3, 4, 4, 4, 1, 0, 0);
    drawRectangleSides(2, 2, 2, 5, 5, 5, 1, 0, 0);
    drawRectangleSides(1, 1, 1, 6, 6, 6, 1, 0, 0);
    drawRectangleSides(0, 0, 0, 7, 7, 7, 0, 0, 0); delay(TD6);
    
    drawRectangleSides(3, 3, 3, 4, 4, 4, 0, 1, 0);
    drawRectangleSides(2, 2, 2, 5, 5, 5, 1, 0, 0);
    drawRectangleSides(1, 1, 1, 6, 6, 6, 1, 0, 0);
    drawRectangleSides(0, 0, 0, 7, 7, 7, 1, 0, 0); delay(TD6);

  for (int count= 0; count < 2; count++) {
    drawRectangleSides(3, 3, 3, 4, 4, 4, 0, 1, 0);
    drawRectangleSides(2, 2, 2, 5, 5, 5, 0, 1, 0);
    drawRectangleSides(1, 1, 1, 6, 6, 6, 1, 0, 0);
    drawRectangleSides(0, 0, 0, 7, 7, 7, 1, 0, 0); delay(TD6);
    
    drawRectangleSides(3, 3, 3, 4, 4, 4, 0, 1, 0);
    drawRectangleSides(2, 2, 2, 5, 5, 5, 0, 1, 0);
    drawRectangleSides(1, 1, 1, 6, 6, 6, 0, 1, 0);
    drawRectangleSides(0, 0, 0, 7, 7, 7, 1, 0, 0); delay(TD6);
    
    drawRectangleSides(3, 3, 3, 4, 4, 4, 0, 0, 1);
    drawRectangleSides(2, 2, 2, 5, 5, 5, 0, 1, 0);
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
    drawRectangleSides(0, 0, 0, 7, 7, 7, 1, 1, 1); delay(TD6);
    
    drawRectangleSides(3, 3, 3, 4, 4, 4, 1, 0, 0);
    drawRectangleSides(2, 2, 2, 5, 5, 5, 1, 0, 0);
    drawRectangleSides(1, 1, 1, 6, 6, 6, 1, 0, 0);
    drawRectangleSides(0, 0, 0, 7, 7, 7, 1, 1, 1); delay(TD6);  

    drawRectangleSides(3, 3, 3, 4, 4, 4, 0, 1, 0);
    drawRectangleSides(2, 2, 2, 5, 5, 5, 1, 0, 0);
    drawRectangleSides(1, 1, 1, 6, 6, 6, 1, 0, 0);
    drawRectangleSides(0, 0, 0, 7, 7, 7, 1, 0, 0); delay(TD6);
    
  }
    
    drawRectangleSides(3, 3, 3, 4, 4, 4, 0, 0, 0);
    drawRectangleSides(2, 2, 2, 5, 5, 5, 1, 1, 1);
    drawRectangleSides(1, 1, 1, 6, 6, 6, 1, 1, 1);
    drawRectangleSides(0, 0, 0, 7, 7, 7, 1, 1, 1); delay(TD6);  
    
    drawRectangleSides(3, 3, 3, 4, 4, 4, 0, 0, 0);
    drawRectangleSides(2, 2, 2, 5, 5, 5, 0, 0, 0);
    drawRectangleSides(1, 1, 1, 6, 6, 6, 1, 1, 1);
    drawRectangleSides(0, 0, 0, 7, 7, 7, 1, 1, 1); delay(TD6);
    
    drawRectangleSides(3, 3, 3, 4, 4, 4, 0, 0, 0);
    drawRectangleSides(2, 2, 2, 5, 5, 5, 0, 0, 0);
    drawRectangleSides(1, 1, 1, 6, 6, 6, 0, 0, 0);
    drawRectangleSides(0, 0, 0, 7, 7, 7, 1, 1, 1); delay(TD6);  
    
    drawRectangleSides(3, 3, 3, 4, 4, 4, 0, 0, 0);
    drawRectangleSides(2, 2, 2, 5, 5, 5, 0, 0, 0);
    drawRectangleSides(1, 1, 1, 6, 6, 6, 0, 0, 0);
    drawRectangleSides(0, 0, 0, 7, 7, 7, 0, 0, 0); delay(TD6);  

} 
// ===================
// ~~~ END of LOOP ~~~
// ===================



// =====================================================================================================
// ~~~ START of DISPLAY SOME TEXT ~~~
// ----------------------------------
//   takes a string of text and displays it one character at a time with each new word a random colour
// =====================================================================================================
void displaySomeText(String someText, int pauseTime) {
  byte aChar;                                 // grabs one character at a time from the message string
  int  stringLen;                             // length of text message
  byte myColour;                              // random colour
  
  uint16_t charScroll[8] = {0x0000, 0x0000,   // 8 row 16 bit display buffer
                            0x0000, 0x0000,   // 8x8 panel maps to the 8 MSB's
                            0x0000, 0x0000,   // aChar loads into 8 LSB's
                            0x0000, 0x0000};  // bit shifts to the left to scroll new char in and old char out
      
  stringLen = someText.length();              // find length of text message
  myColour = random(7) + 1;                   // select first random colour

  for(int i = 0; i < stringLen; i++){         // loop for as many characters in text message
    aChar = int(someText[i] - 0x20);          // get ascii value for each character and remove offset
    
    // load a character into buffers 8 Least Significant Bits
    for(int j = 0; j < 8; j++){
      charScroll[j] += font8x8_basic[aChar][7 - j] << 8;
    } 
    
    // shift buffer left one bit then load shift registers with the buffers 8 Most Significant Bits
    for(int j = 0; j < 7; j++){
      for(int k = 0; k < 8; k++){
        charScroll[k] = charScroll[k] >> 1;
        if(myColour & 0x01) {shiftRegisterRed[k] = 0x00ff & charScroll[k];} else {shiftRegisterRed[k] = 0;}
        if(myColour & 0x02) {shiftRegisterGrn[k] = 0x00ff & charScroll[k];} else {shiftRegisterGrn[k] = 0;}
        if(myColour & 0x04) {shiftRegisterBlu[k] = 0x00ff & charScroll[k];} else {shiftRegisterBlu[k] = 0;}
      }
      delay(60);
    }
    // if a space is detected chose a new random colour for the next word
    if(aChar == 0x00){ myColour = random(7) + 1; }
  }
delay(1000);
} 
// ================================
// ~~~ END of DISPLAY SOME TEXT ~~~
// ================================



// =====================================================================================================
// ~~~ START Draw Rectanle Outline ~~~
// -----------------------------------
// draw a 3d wireframe rectangle 
// =====================================================================================================
void drawRectangleOutline(int xMin, int yMin , int zMin, int xMax, int yMax, int zMax, boolean red, boolean grn, boolean blu) {

  for (int x = xMin; x < xMax + 1; x++) {
    setPixel( x, yMin, zMin, red, grn, blu);
    setPixel( x, yMin, zMax, red, grn, blu);
    setPixel( x, yMax, zMax, red, grn, blu);
    setPixel( x, yMax, zMin, red, grn, blu);
  }
  for (int y = yMin; y < yMax + 1; y++) {
    setPixel( xMin, y, zMin, red, grn, blu);
    setPixel( xMin, y, zMax, red, grn, blu);
    setPixel( xMax, y, zMax, red, grn, blu);
    setPixel( xMax, y, zMin, red, grn, blu);
  }
  for (int z = zMin; z < zMax + 1; z++) {
    setPixel( xMin, yMin, z, red, grn, blu);
    setPixel( xMin, yMax, z, red, grn, blu);
    setPixel( xMax, yMax, z, red, grn, blu);
    setPixel( xMax, yMin, z, red, grn, blu);
  }
}
// =================================
// ~~~ END Draw Rectanle Outline ~~~
// =================================



// =====================================================================================================
// ~~~ START Draw Rectanle Sides ~~~
// ---------------------------------
// draw a 3d rectangle filled sides 
// =====================================================================================================
void drawRectangleSides(int xMin, int yMin , int zMin, int xMax, int yMax, int zMax, boolean red, boolean grn, boolean blu) {

  for (int x = xMin; x < xMax + 1; x++) {
    for (int y = yMin; y < yMax + 1; y++) {
      setPixel( x, y, zMin, red, grn, blu);
      setPixel( x, y, zMax, red, grn, blu);
    }
  }
  for (int y = yMin; y < yMax + 1; y++) {
    for (int z = zMin; z < zMax + 1; z++) {
      setPixel( xMin, y, z, red, grn, blu);
      setPixel( xMax, y, z, red, grn, blu);
    }
  }
  for (int x = xMin; x < xMax + 1; x++) {
    for (int z = zMin; z < zMax + 1; z++) {
      setPixel( x, yMin, z, red, grn, blu);
      setPixel( x, yMax, z, red, grn, blu);
    }
  }
}
// ===============================
// ~~~ END Draw Rectanle Sides ~~~
// ===============================



// =====================================================================================================
// ~~~ START Draw Rectanle Filled ~~~
// ----------------------------------
// draw a 3d rectangle filled 
// =====================================================================================================
void drawRectangleFilled(int xMin, int yMin , int zMin, int xMax, int yMax, int zMax, boolean red, boolean grn, boolean blu) {

  for (int x = xMin; x < xMax + 1; x++) {
    for (int y = yMin; y < yMax + 1; y++) {
      for (int z = zMin; z < zMax + 1; z++) {
        setPixel(x, y, z, red, grn, blu);
      }
    }
  }
}
// ================================
// ~~~ END Draw Rectanle Filled ~~~
// ================================



// =====================================================================================================
// ~~~ Start Flood Fill ~~~
// ------------------------
// fills entire panel with chosen colour via direct manipulation of the shift register arrays 
// (much faster than setting individual pixels)
// =====================================================================================================
void floodFill(boolean red, boolean grn, boolean blu) {

  for ( int indexY = 0; indexY < 8; indexY++ ) {
    if(red == 1) {shiftRegisterRed[indexY] = B11111111;} else {shiftRegisterRed[indexY] = B00000000;}
    if(grn == 1) {shiftRegisterGrn[indexY] = B11111111;} else {shiftRegisterGrn[indexY] = B00000000;}
    if(blu == 1) {shiftRegisterBlu[indexY] = B11111111;} else {shiftRegisterBlu[indexY] = B00000000;}
  }
}
// =========================
// ~~~ END of Flood Fill ~~~
// =========================



// =====================================================================================================
// ~~~ Start Fill YZ Axis Plane ~~~
// --------------------------------
// 
// 
// =====================================================================================================
void yzPlaneFill(byte xIndex, byte colour) {
  
  boolean red = colour & B00000001; 
  boolean grn = colour & B00000010; 
  boolean blu = colour & B00000100;
  Serial.print("red = ");
  Serial.print(red);
  
  // test column index is within boundary
  if ( xIndex < 0) xIndex = 0;
  if ( xIndex > 7) xIndex = 7;  
  
  // set the register arrays using bit manipulation
  for ( int i = 0; i < 8; i++ ) {
    for ( int j = 0; j < 8; j++ ) {
      if ( red == 0 ) shiftRegisterRed[i + (j * 8)] &= ~(1 << xIndex); else shiftRegisterRed[i + (j * 8)] |=  (1 << xIndex);
      if ( grn == 0 ) shiftRegisterGrn[i + (j * 8)] &= ~(1 << xIndex); else shiftRegisterGrn[i + (j * 8)] |=  (1 << xIndex);
      if ( blu == 0 ) shiftRegisterBlu[i + (j * 8)] &= ~(1 << xIndex); else shiftRegisterBlu[i + (j * 8)] |=  (1 << xIndex);  
    }
  }
}
// ==============================
// ~~~ END Fill YZ Axis Plane ~~~
// ==============================



// =====================================================================================================
// ~~~ Start Fill XZ Axis Plane ~~~
// --------------------------------
// 
// 
// =====================================================================================================
void xzPlaneFill(byte yIndex, byte colour) {
  
  boolean red = colour & B00000001; 
  boolean grn = colour & B00000010; 
  boolean blu = colour & B00000100;
  Serial.print("red = ");
  Serial.print(red);
  
  // test column index is within boundary
  if ( yIndex < 0 ) yIndex = 0;
  if ( yIndex > 7 ) yIndex = 7;  
  
  // set the register arrays using bit manipulation
  for (int i = 0; i < 8; i++) {
    if(red == 0) {shiftRegisterRed[i + (yIndex * 8)] = 0;} else {shiftRegisterRed[i + (yIndex * 8)] = 255;}
    if(grn == 0) {shiftRegisterGrn[i + (yIndex * 8)] = 0;} else {shiftRegisterGrn[i + (yIndex * 8)] = 255;}
    if(blu == 0) {shiftRegisterBlu[i + (yIndex * 8)] = 0;} else {shiftRegisterBlu[i + (yIndex * 8)] = 255;} 
  }
}
// ==============================
// ~~~ END Fill XZ Axis Plane ~~~
// ==============================



// =====================================================================================================
// ~~~ Start Fill XZ Axis Plane ~~~
// --------------------------------
// 
// 
// =====================================================================================================
void xyPlaneFill(byte zIndex, byte colour) {
  
  boolean red = colour & B00000001; 
  boolean grn = colour & B00000010; 
  boolean blu = colour & B00000100;
  
  // test column index is within boundary
  if ( zIndex < 0 ) zIndex = 0;
  if ( zIndex > 7 ) zIndex = 7;  
  
  // set the register arrays using bit manipulation
  for ( int i = 0; i < 8; i++ ) {
    if ( red == 0 ) {shiftRegisterRed[zIndex + ( 8 * i)] = 0;} else {shiftRegisterRed[zIndex + ( 8 * i)] = 255;}
    if ( grn == 0 ) {shiftRegisterGrn[zIndex + ( 8 * i)] = 0;} else {shiftRegisterGrn[zIndex + ( 8 * i)] = 255;}
    if ( blu == 0 ) {shiftRegisterBlu[zIndex + ( 8 * i)] = 0;} else {shiftRegisterBlu[zIndex + ( 8 * i)] = 255;} 
  }
}
// =======================
// ~~~ END of Fill Row ~~~
// =======================



// =====================================================================================================
// ~~~ Start Set Pixel ~~~
// -----------------------
// take a pixels x & y co-ordinate, R, G & B binary values and assigns to appropriate shift register bit
// =====================================================================================================
void setPixel(byte pixelX, byte pixelY, byte pixelZ, boolean red, boolean grn, boolean blu) {

  // test pixel x & co-ordinates are within boundary
  if(pixelX < 0) pixelX = 0;
  if(pixelX > 7) pixelX = 7;
  if(pixelY < 0) pixelY = 0;
  if(pixelY > 7) pixelY = 7;
  if(pixelZ < 0) pixelZ = 0;
  if(pixelZ > 7) pixelZ = 7;
  
  // set appropriate registers using bit manipulation.
  // just Google 'bit shifting in c' 
  // to find tutorials and explanations of the following:  
  if(red == 1) shiftRegisterRed[(8 * pixelY) + (7 - pixelZ)] |=  (1 << pixelX);   // if red is 1 set appropriate bit within appropriate red byte to 1
    else       shiftRegisterRed[(8 * pixelY) + (7 - pixelZ)] &= ~(1 << pixelX);   //   otherwise set appropriate bit within appropriate red byte to 0
    
  if(grn == 1) shiftRegisterGrn[(8 * pixelY) + (7 - pixelZ)] |=  (1 << pixelX);   // if grn is 1 set appropriate bit within appropriate grn byte to 1 
    else       shiftRegisterGrn[(8 * pixelY) + (7 - pixelZ)] &= ~(1 << pixelX);   //   otherwise set appropriate bit within appropriate grn byte to 0
    
  if(blu == 1) shiftRegisterBlu[(8 * pixelY) + (7 - pixelZ)] |=  (1 << pixelX);   // if blu is 1 set appropriate bit within appropriate blu byte to 1
    else       shiftRegisterBlu[(8 * pixelY) + (7 - pixelZ)] &= ~(1 << pixelX);   //   otherwise set appropriate bit within appropriate blu byte to 0
}
// ======================
// ~~~ END Set Pixel  ~~~
// ======================



// =====================================================================================================
// ~~~ START 0f ISR ~~~
// --------------------
//   Updates the panel. Called every 125uS (8KHz), each row is lit for 1/8th of the time (1KHz)
// =====================================================================================================
ISR(TIMER2_COMPA_vect) {
  
  PORTD |= (1 << SR_BLANK);                      // temporarely disable the SR outputs
for (int i = 0; i < 8; i++) {
  SPI.transfer(shiftRegisterRed[i + anodeIndex * 8]);    // send the red SR byte for the given anode level
  SPI.transfer(shiftRegisterGrn[i + anodeIndex * 8]);    // send the grn SR byte for the given anode level
  SPI.transfer(shiftRegisterBlu[i + anodeIndex * 8]);    // send the blu SR byte for the given anode level
}
  SPI.transfer(anodeLevel[anodeIndex]);          // send the anode multiplex byte
  anodeIndex = (anodeIndex + 1) % 8;             // incrument anode index ready for next ISR
  PORTD |=  (1 << SR_LATCH);                     // set latch pin LOW
  PORTD &= ~(1 << SR_LATCH);                     // set latch pin HIGH - SR outputs now have new data
  PORTD &= ~(1 << SR_BLANK);                     // re-enable the SR outputs
}
// ==================
// ~~~ END of ISR ~~~
// ==================



/*
* Copyright (c) 2014 Steve Manley
*
* Permission is hereby granted, free of charge, to any person obtaining a copy
* of this software and associated documentation files (the "Software"), to deal
* in the Software without restriction, including without limitation the rights
* to use, copy, modify, merge, publish, distribute, sublicense, and/or sell
* copies of the Software, and to permit persons to whom the Software is
* furnished to do so, subject to the following conditions:
*
* The above copyright notice and this permission notice shall be included in
* all copies or substantial portions of the Software.
*
* THE SOFTWARE IS PROVIDED "AS IS", WITHOUT WARRANTY OF ANY KIND, EXPRESS OR
* IMPLIED, INCLUDING BUT NOT LIMITED TO THE WARRANTIES OF MERCHANTABILITY,
* FITNESS FOR A PARTICULAR PURPOSE AND NONINFRINGEMENT. IN NO EVENT SHALL THE
* AUTHOR(S) OR COPYRIGHT HOLDER(S) BE LIABLE FOR ANY CLAIM, DAMAGES OR OTHER
* LIABILITY, WHETHER IN AN ACTION OF CONTRACT, TORT OR OTHERWISE, ARISING FROM,
* OUT OF OR IN CONNECTION WITH THE SOFTWARE OR THE USE OR OTHER DEALINGS IN
* THE SOFTWARE.
*/
