joelamichaelis/8x8x8_RGB_LED_CUBE/Project Photos/Phase 1 Cube Build/03 Vertical Panel Making/20180319_184419.jpg

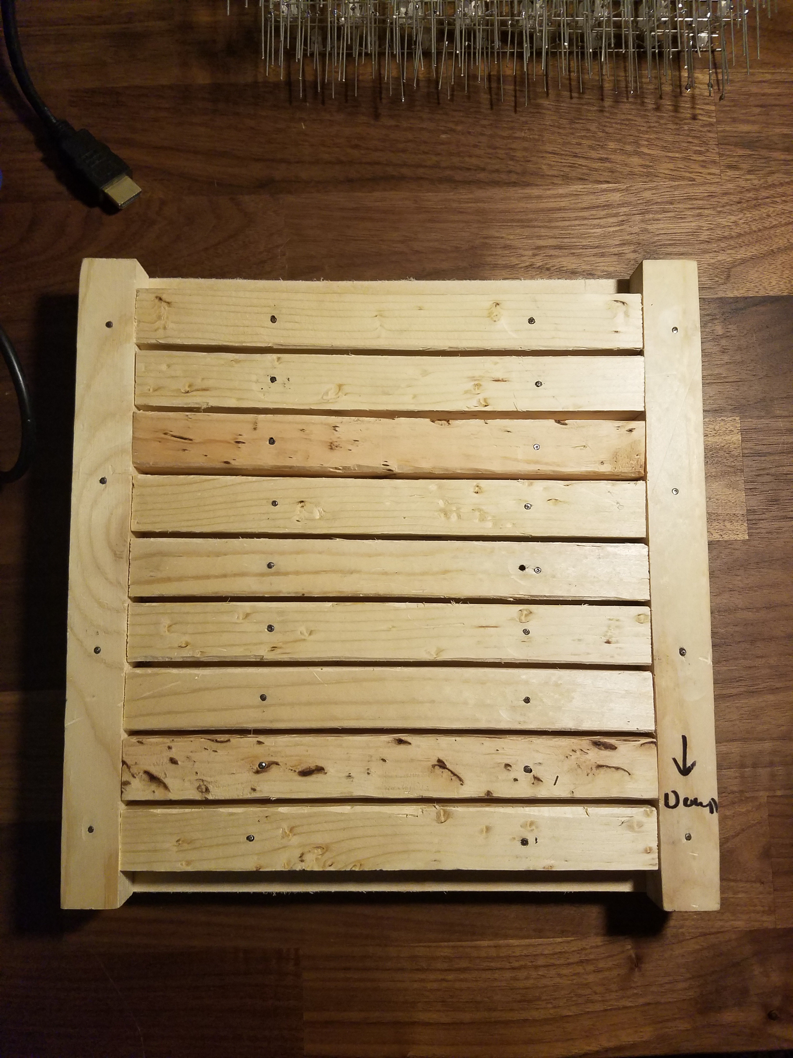
Project Photos/Phase 1 Cube Build/03 Vertical Panel Making/20180319_184419.jpg
