joelamichaelis/8x8x8_RGB_LED_CUBE/Project Photos/Phase 1 Cube Build/05 Wiring & Electronics Integration/20180813_184110.jpg

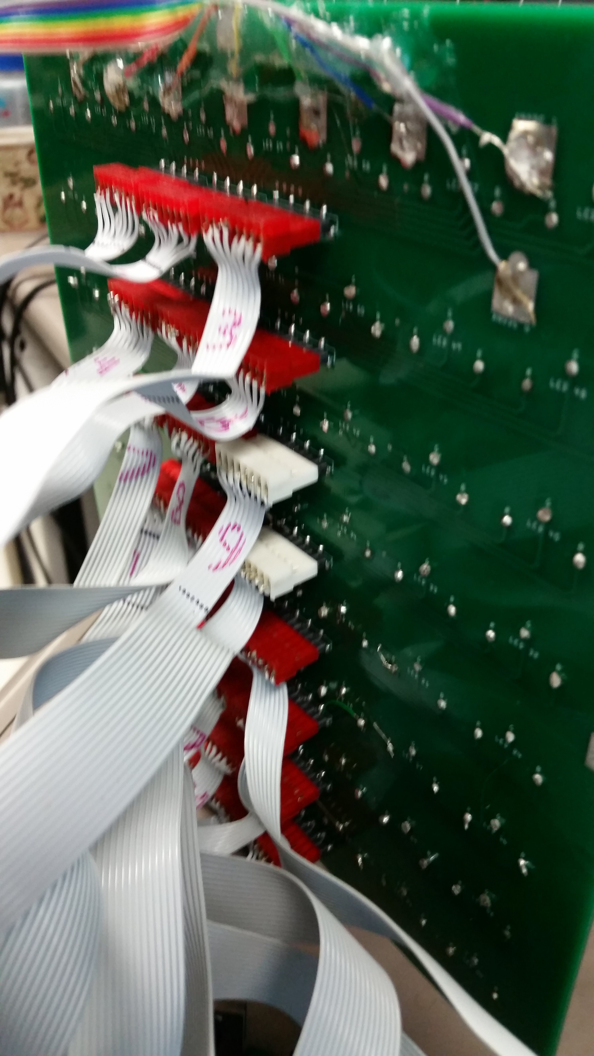
Project Photos/Phase 1 Cube Build/05 Wiring & Electronics Integration/20180813_184110.jpg
